davewhiiite/wraith/images/IMG_1542.jpg

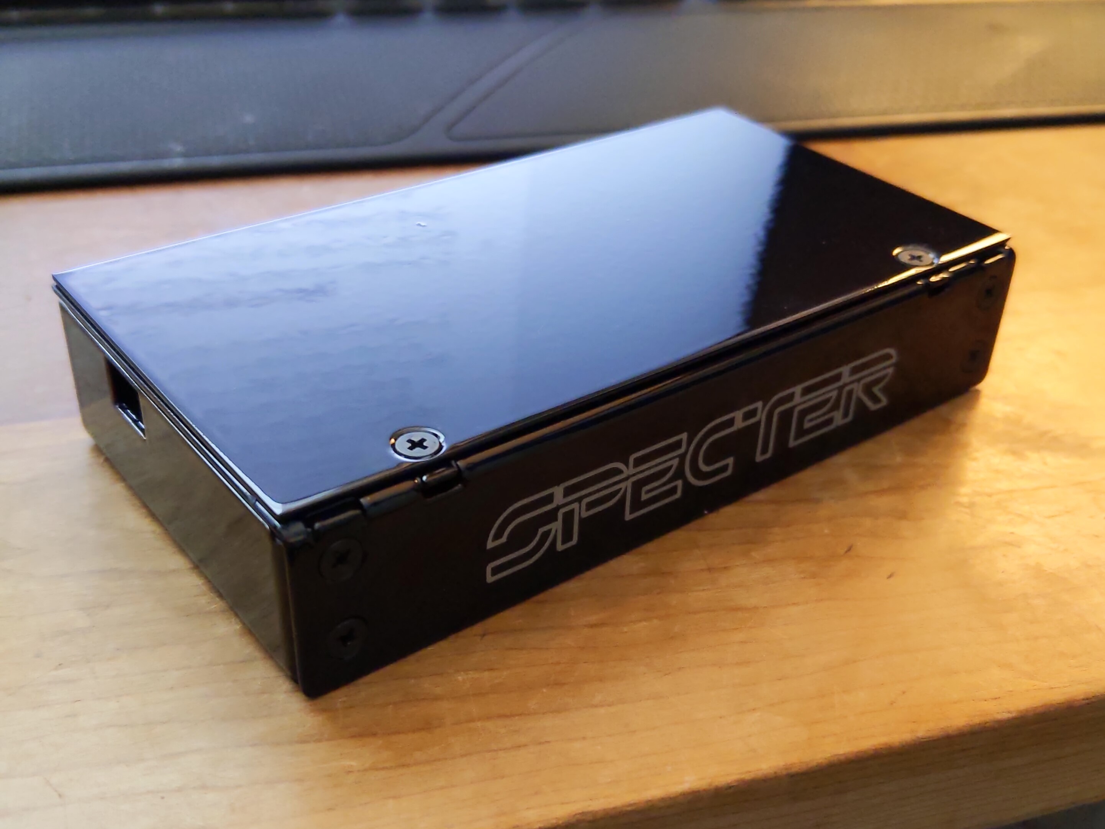
images/IMG_1542.jpg
