davewhiiite/wraith/images/IMG_2205.jpg

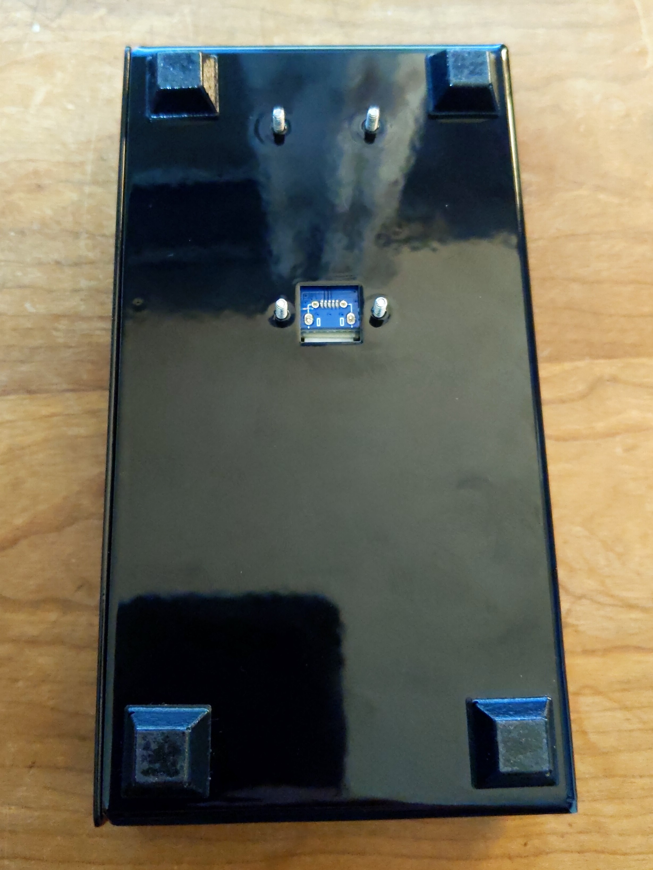
images/IMG_2205.jpg
