davewhiiite/wraith/images/IMG_4864.jpg

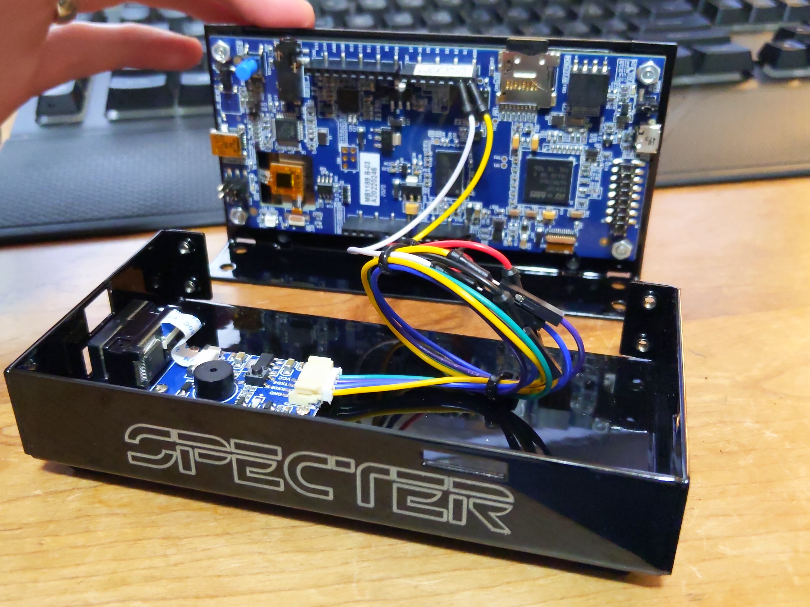
images/IMG_4864.jpg
