davewhiiite/wraith/images/IMG_12469.jpg

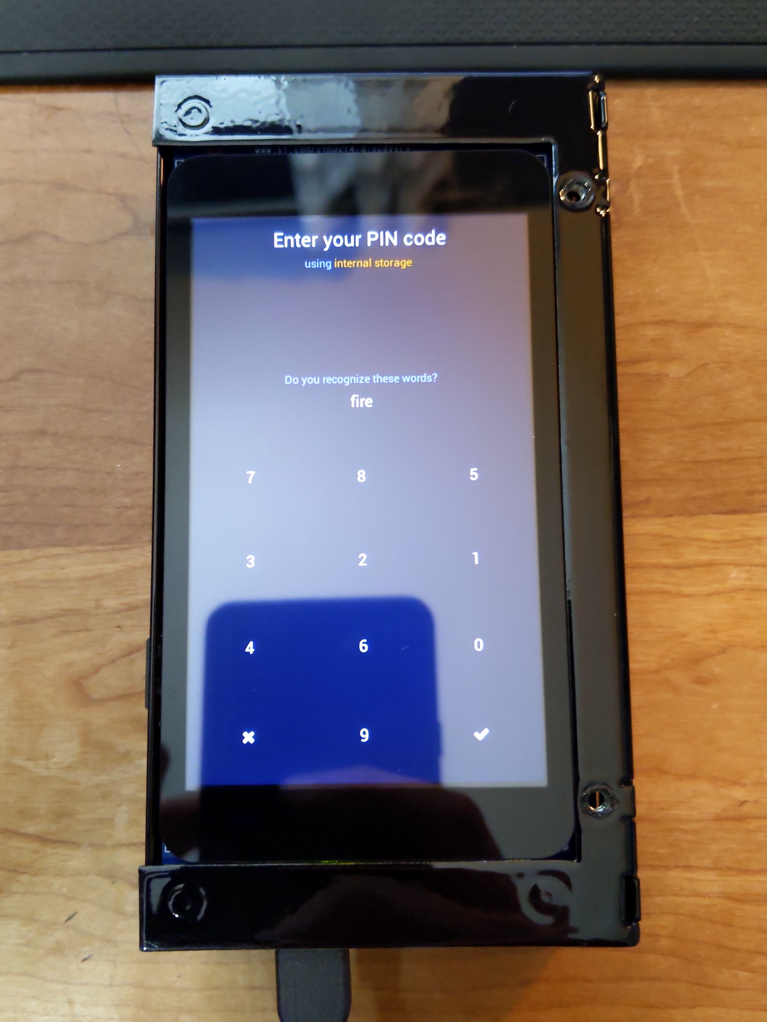
images/IMG_12469.jpg
