davewhiiite/wraith/images/IMG_15060.jpg

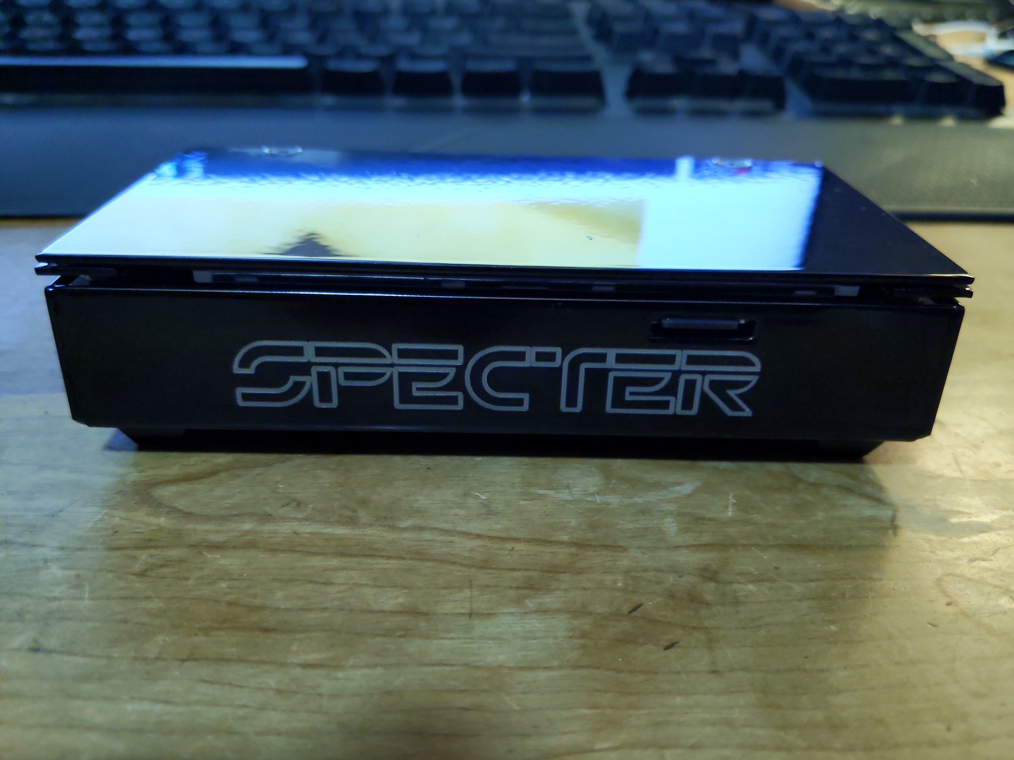
images/IMG_15060.jpg
