davewhiiite/wraith/images/IMG_26794.jpg

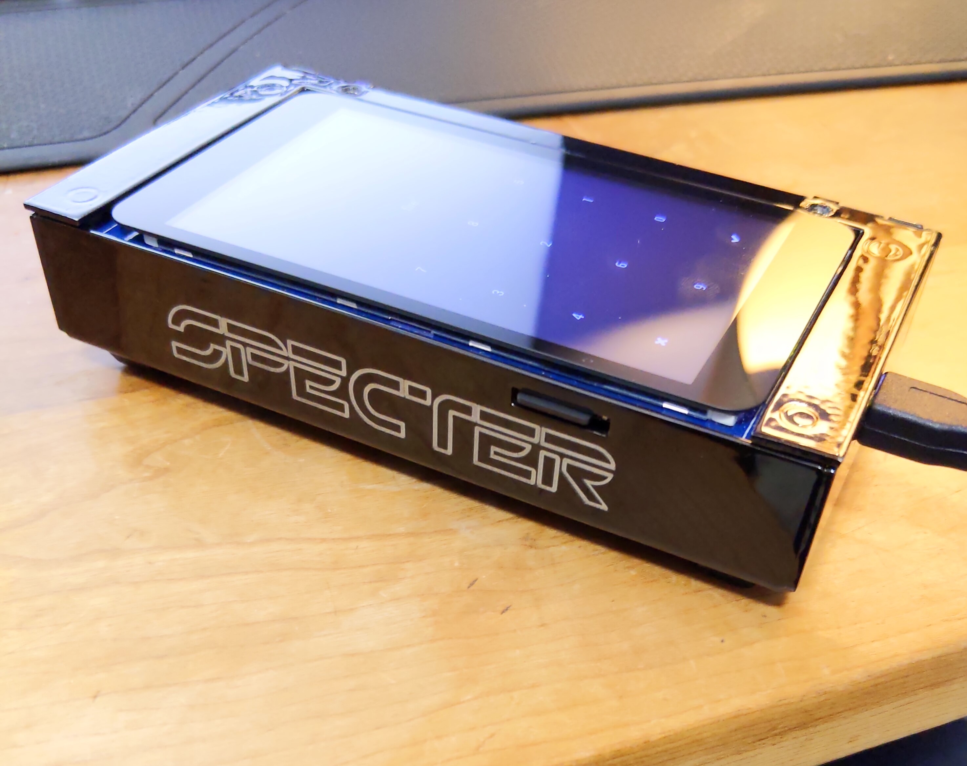
images/IMG_26794.jpg
