davewhiiite/wraith/images/IMG_27332.jpg

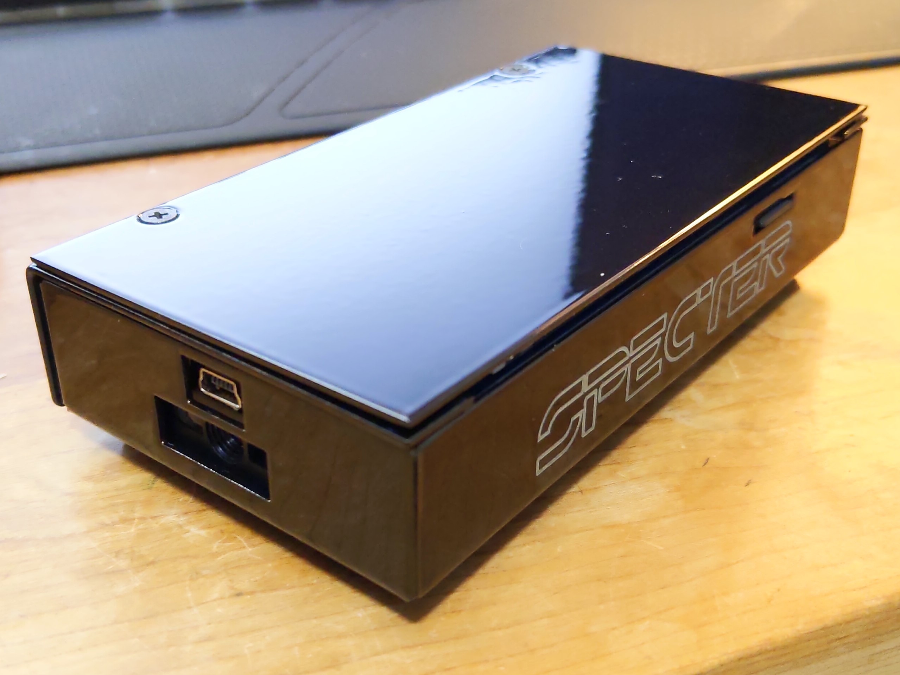
images/IMG_27332.jpg
