davewhiiite/wraith/images/IMG_30229.jpg

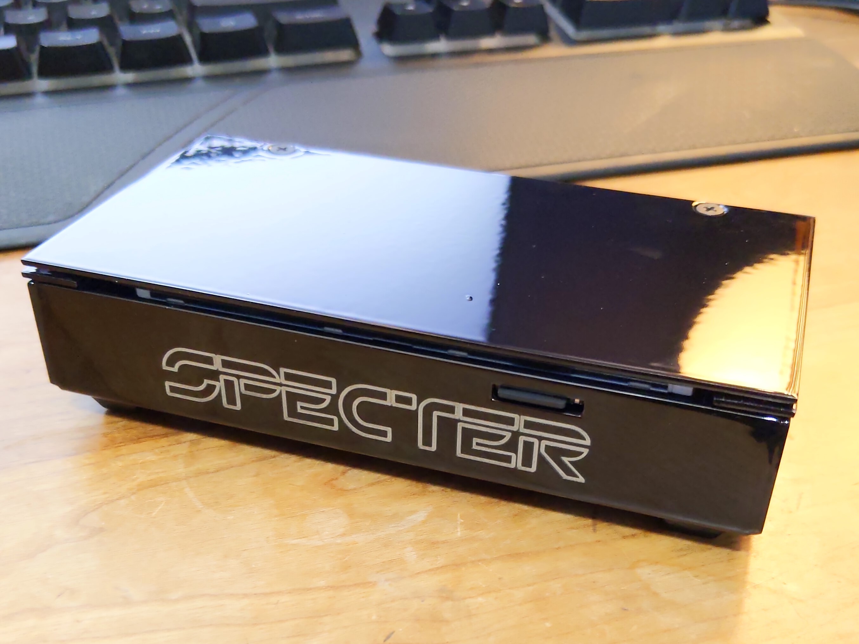
images/IMG_30229.jpg
