davewhiiite/wraith/images/IMG_30313.jpg

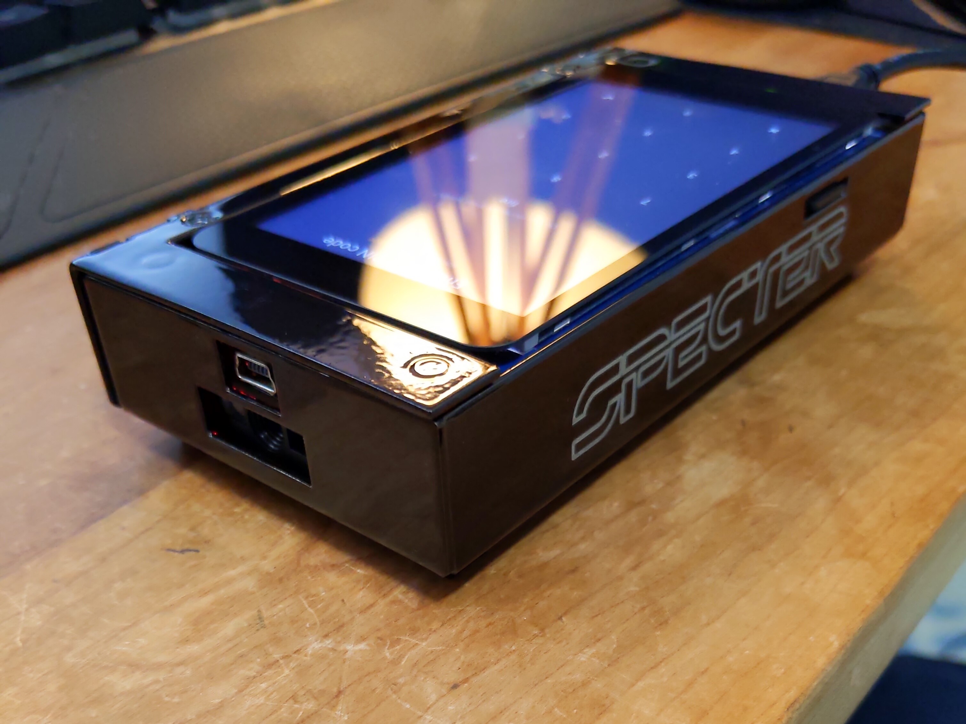
images/IMG_30313.jpg
