davewhiiite/wraith/wraith-assy/95495K421_POLYURETHANE RUBBER ADHESIVE-BACK BUMPER.SLDPRT

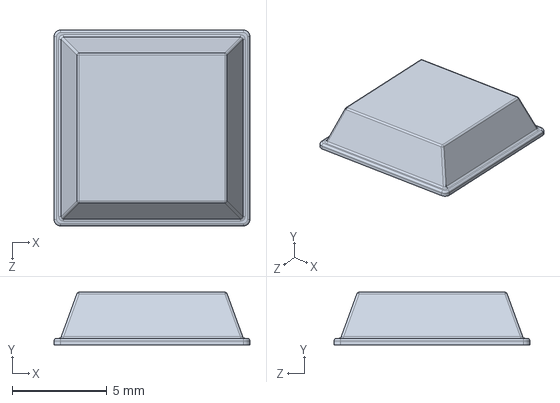
[picture p28: CAD file, 2020-12-21]
wraith-assy/95495K421_POLYURETHANE RUBBER ADHESIVE-BACK BUMPER.SLDPRT
10.3 x 2.78 x 10.3 mm
